LoganCoop/New-Paltz-Capstone-Project/calib_images/img1.jpg

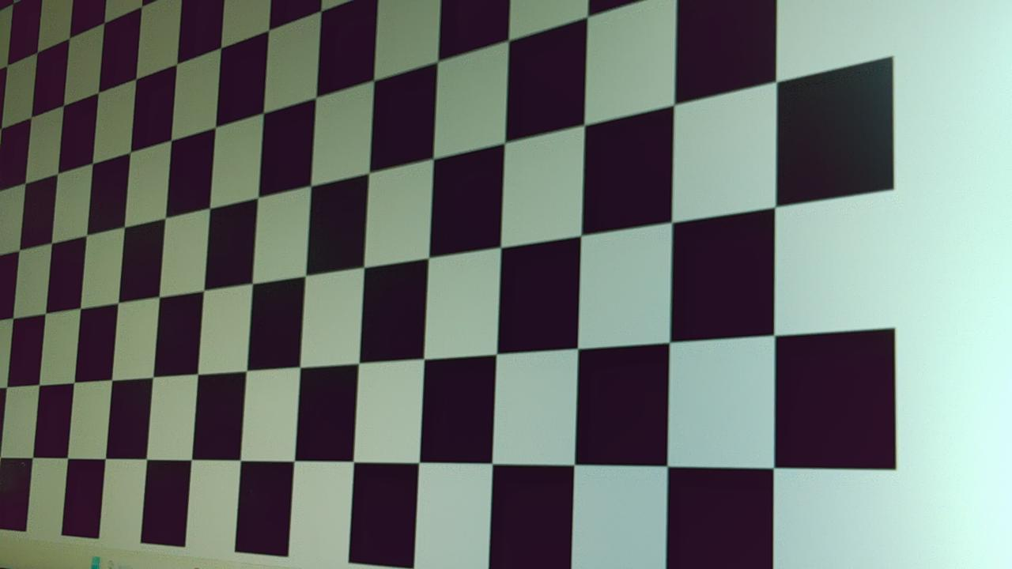
calib_images/img1.jpg
