LoganCoop/New-Paltz-Capstone-Project/calib_images/img01.jpg

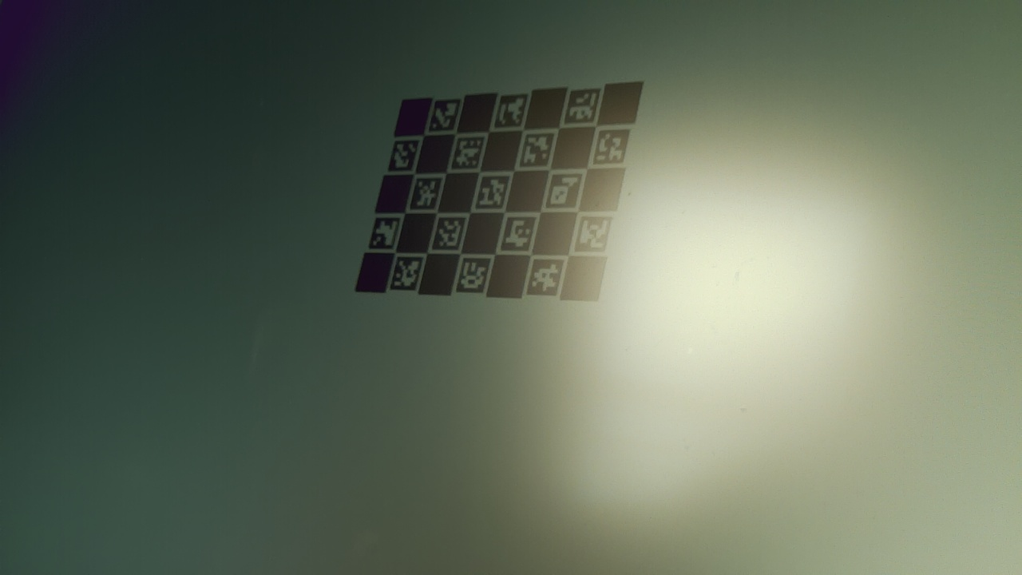
calib_images/img01.jpg
