LoganCoop/New-Paltz-Capstone-Project/calib_images/img2.jpg

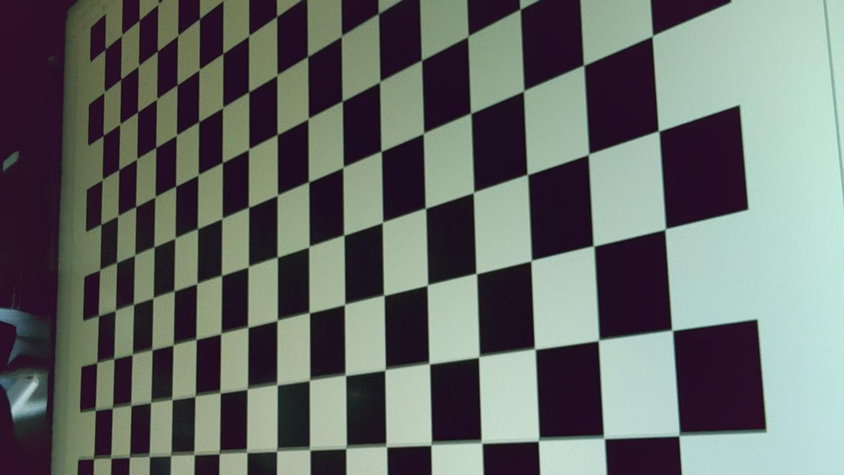
calib_images/img2.jpg
