LoganCoop/New-Paltz-Capstone-Project/calib_images/img03.jpg

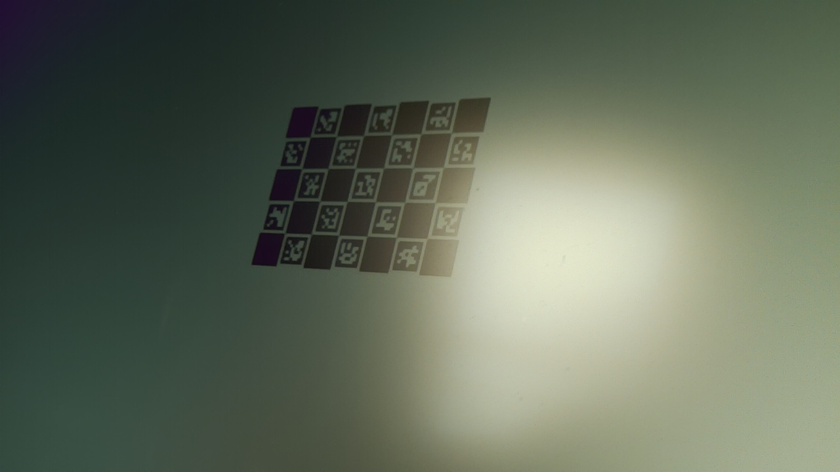
calib_images/img03.jpg
