LoganCoop/New-Paltz-Capstone-Project/calib_images/img3.jpg

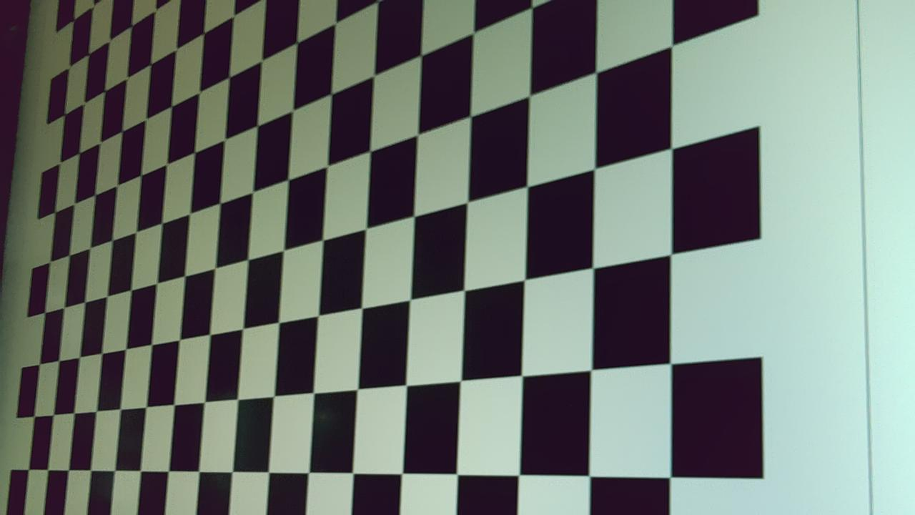
calib_images/img3.jpg
