LoganCoop/New-Paltz-Capstone-Project/calib_images/img4.jpg

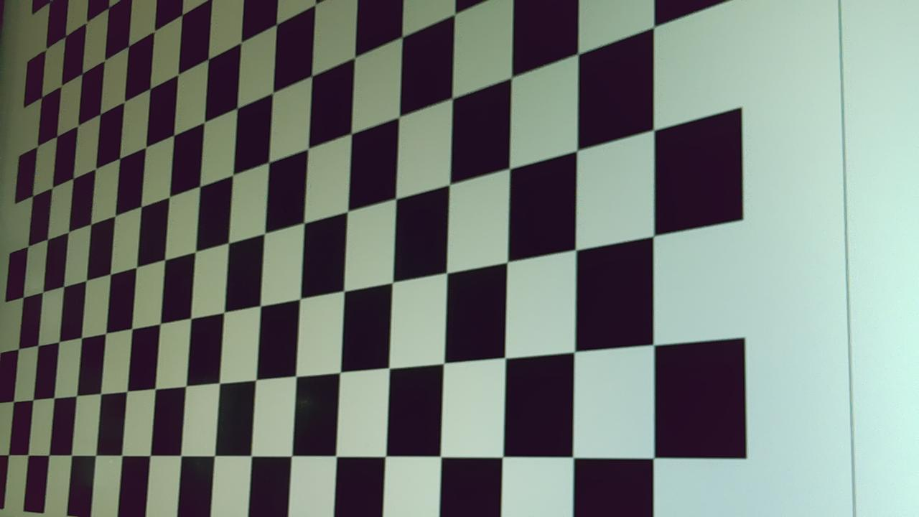
calib_images/img4.jpg
