LoganCoop/New-Paltz-Capstone-Project/calib_images/img5.jpg

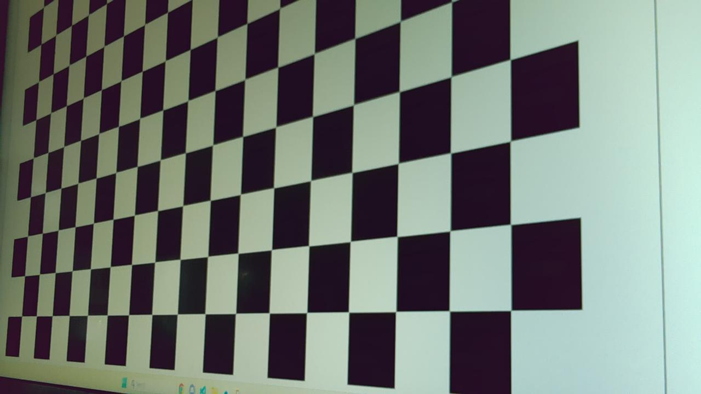
calib_images/img5.jpg
