LoganCoop/New-Paltz-Capstone-Project/calib_images/img05.jpg

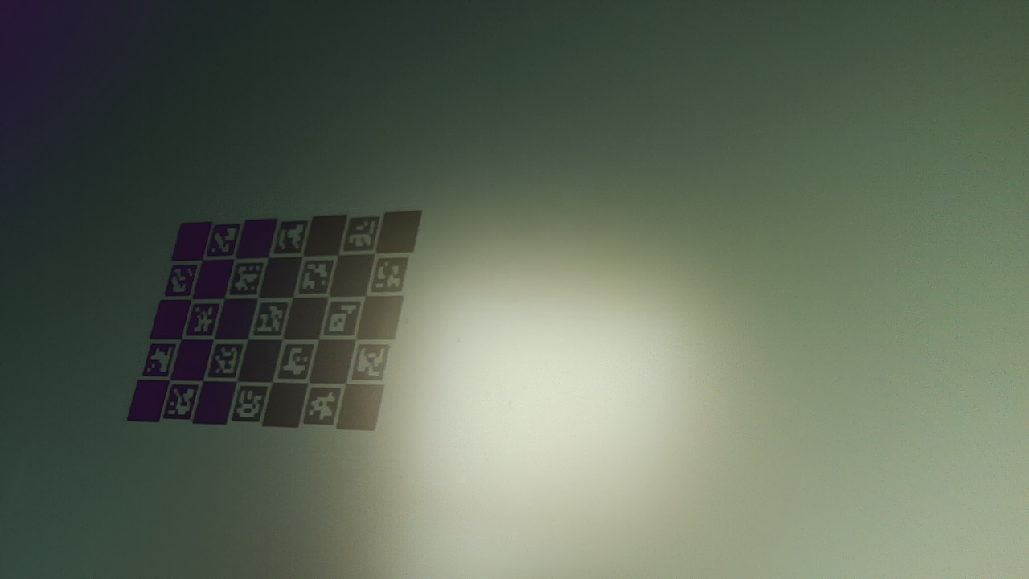
calib_images/img05.jpg
