LoganCoop/New-Paltz-Capstone-Project/calib_images/img06.jpg

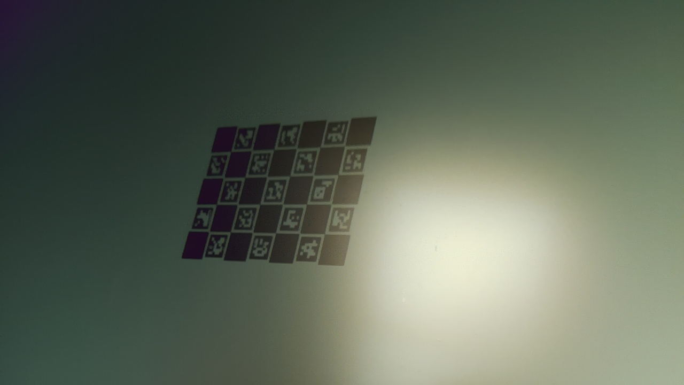
calib_images/img06.jpg
