LoganCoop/New-Paltz-Capstone-Project/calib_images/img6.jpg

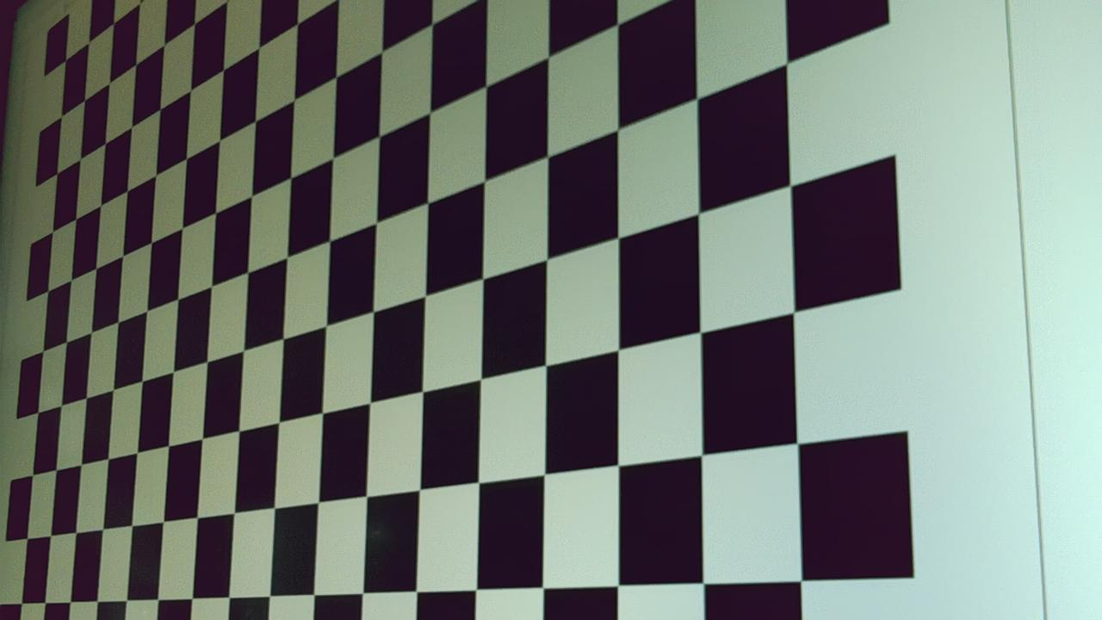
calib_images/img6.jpg
