LoganCoop/New-Paltz-Capstone-Project/calib_images/img07.jpg

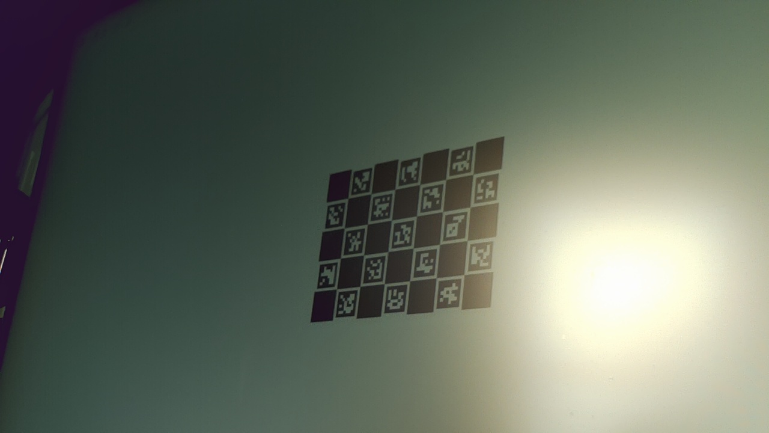
calib_images/img07.jpg
