LoganCoop/New-Paltz-Capstone-Project/calib_images/img7.jpg

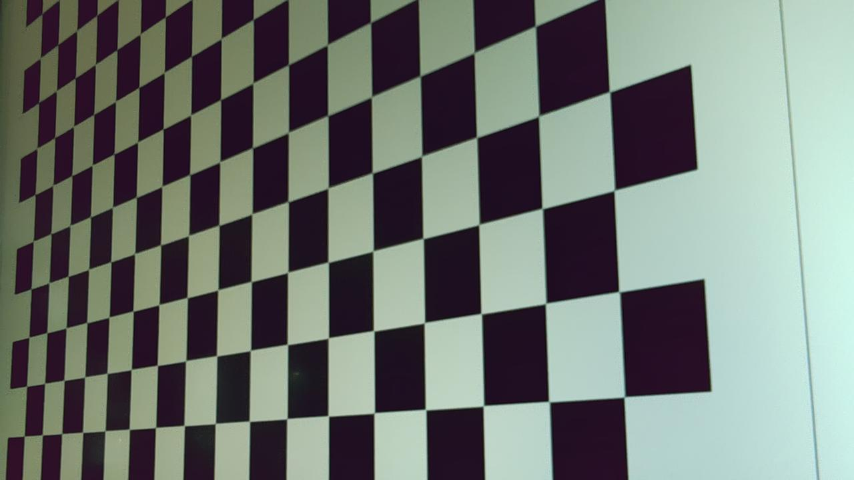
calib_images/img7.jpg
