LoganCoop/New-Paltz-Capstone-Project/calib_images/img8.jpg

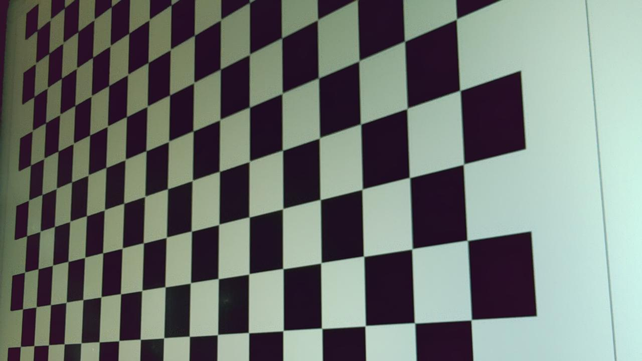
calib_images/img8.jpg
