LoganCoop/New-Paltz-Capstone-Project/calib_images/img08.jpg

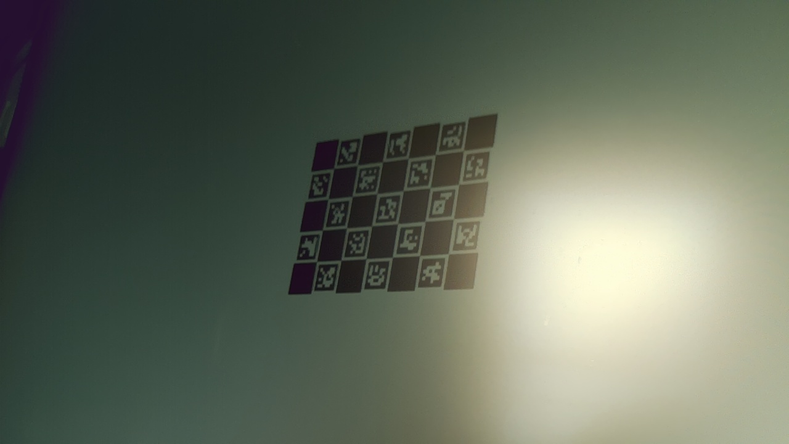
calib_images/img08.jpg
