LoganCoop/New-Paltz-Capstone-Project/calib_images/img9.jpg

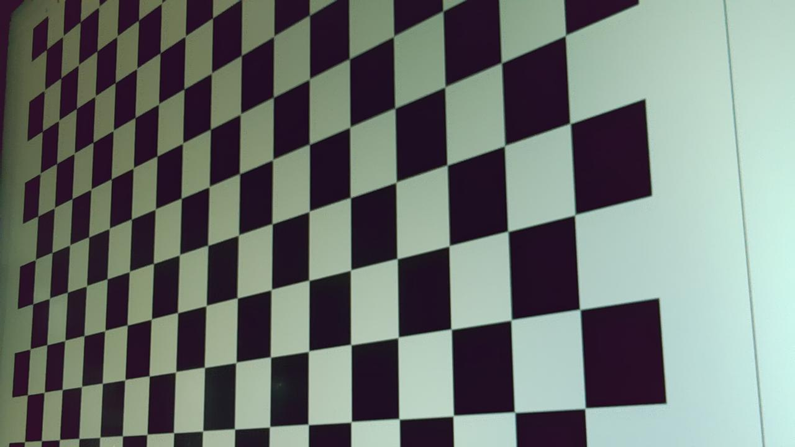
calib_images/img9.jpg
