LoganCoop/New-Paltz-Capstone-Project/calib_images/img09.jpg

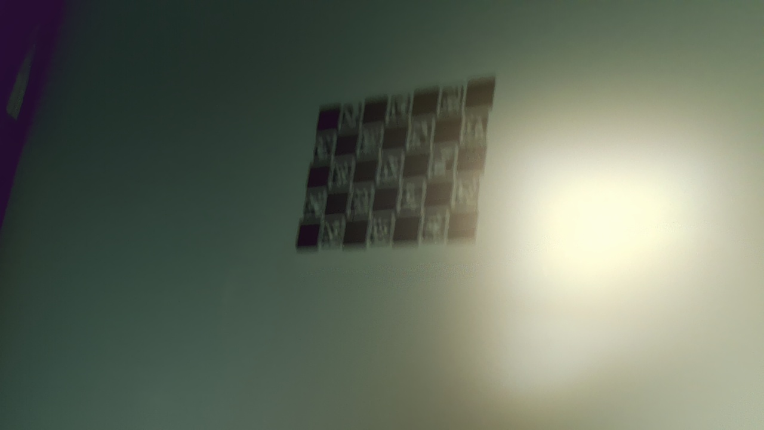
calib_images/img09.jpg
