LoganCoop/New-Paltz-Capstone-Project/calib_images/img10.jpg

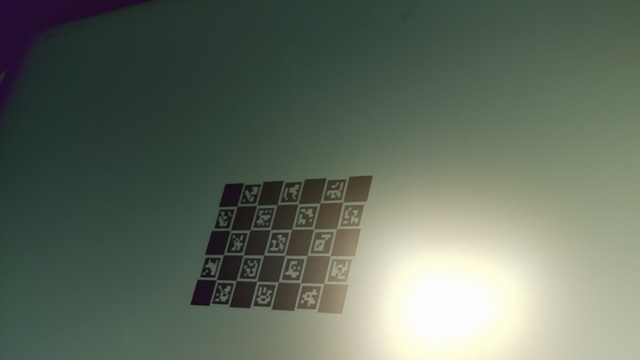
calib_images/img10.jpg
