LoganCoop/New-Paltz-Capstone-Project/calib_images/img11.jpg

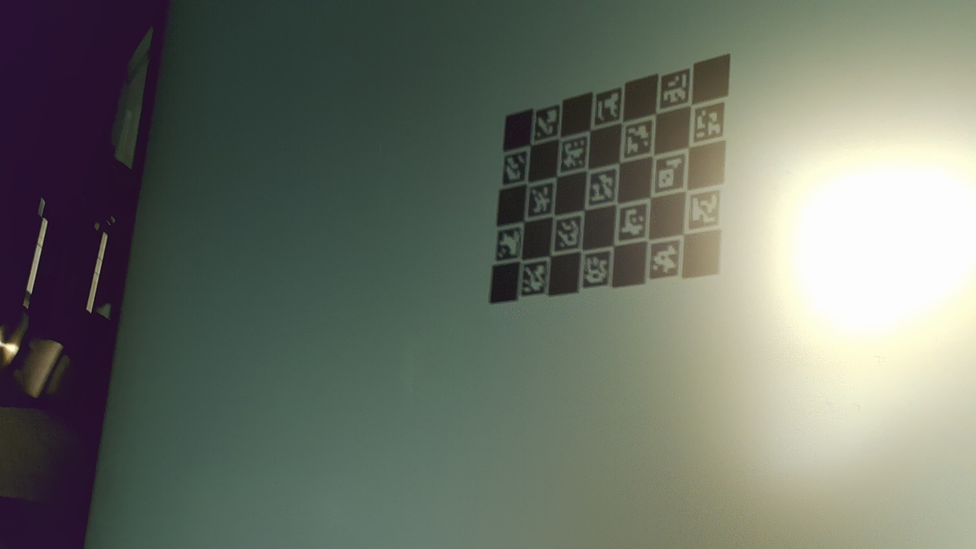
calib_images/img11.jpg
