LoganCoop/New-Paltz-Capstone-Project/calib_images/img12.jpg

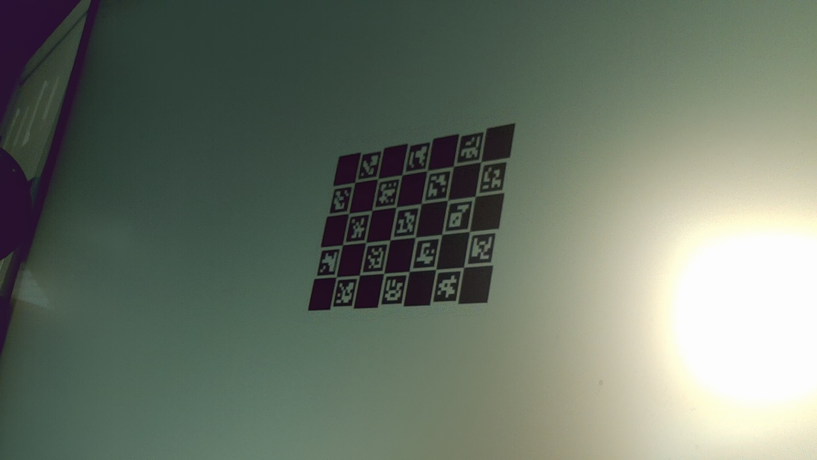
calib_images/img12.jpg
