LoganCoop/New-Paltz-Capstone-Project/calib_images/img14.jpg

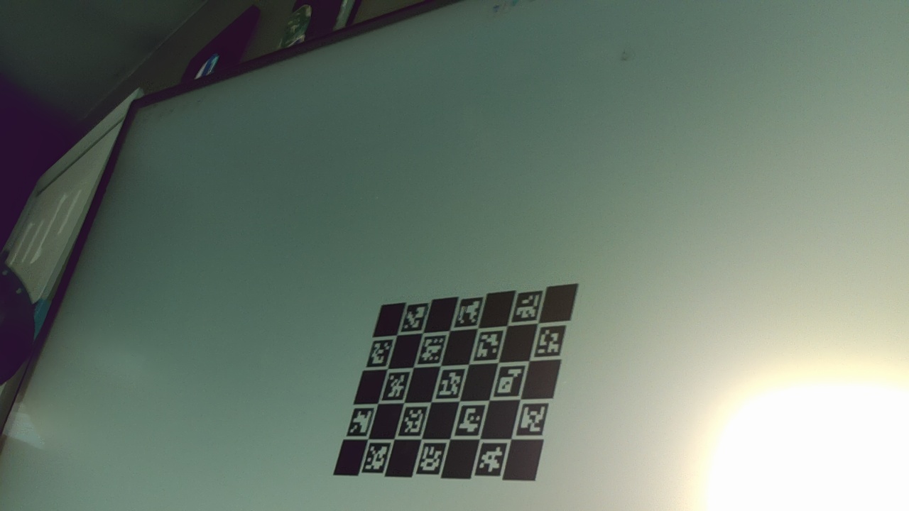
calib_images/img14.jpg
