LoganCoop/New-Paltz-Capstone-Project/calib_images/img15.jpg

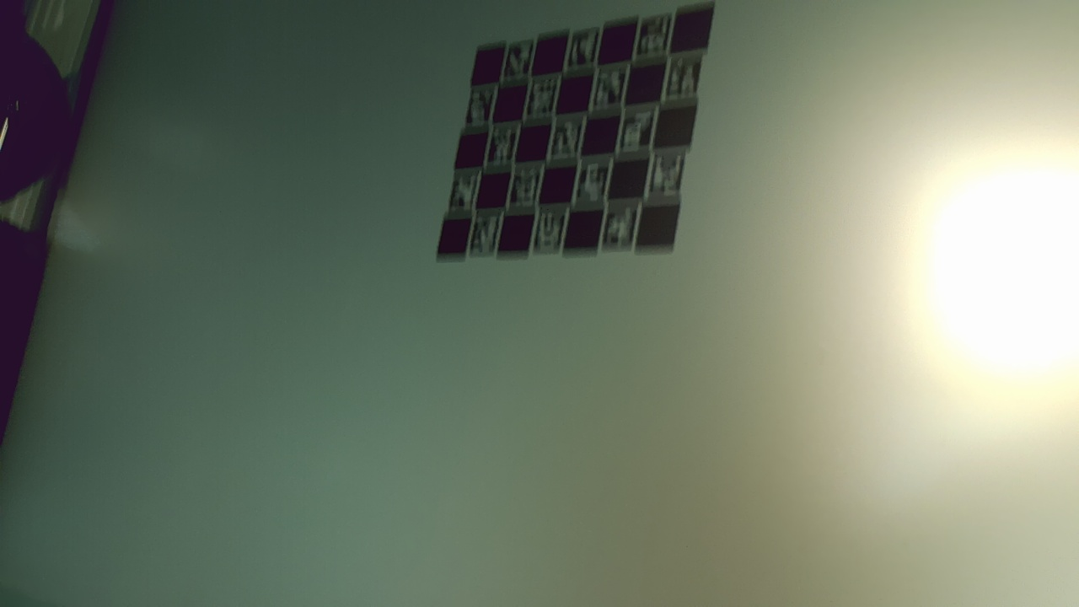
calib_images/img15.jpg
