LoganCoop/New-Paltz-Capstone-Project/calib_images/img100.jpg

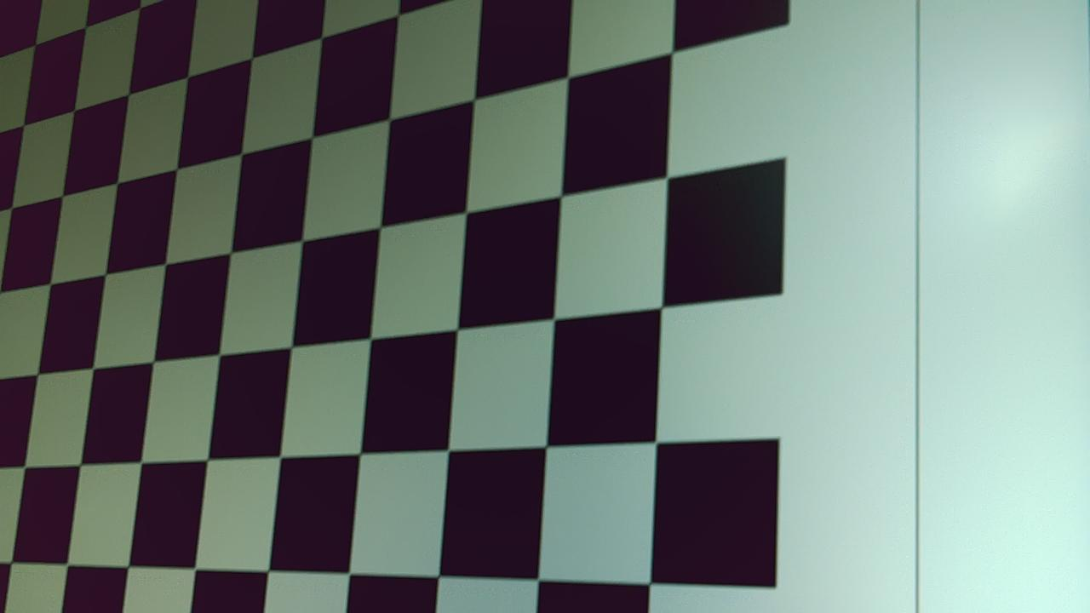
calib_images/img100.jpg
