LoganCoop/New-Paltz-Capstone-Project/calib_images/img101.jpg

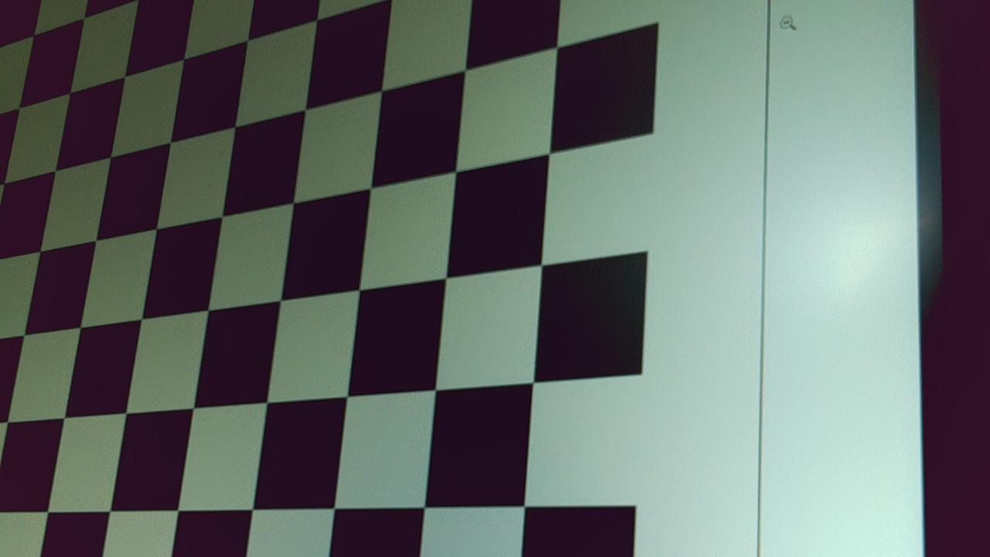
calib_images/img101.jpg
