LoganCoop/New-Paltz-Capstone-Project/calib_images/img102.jpg

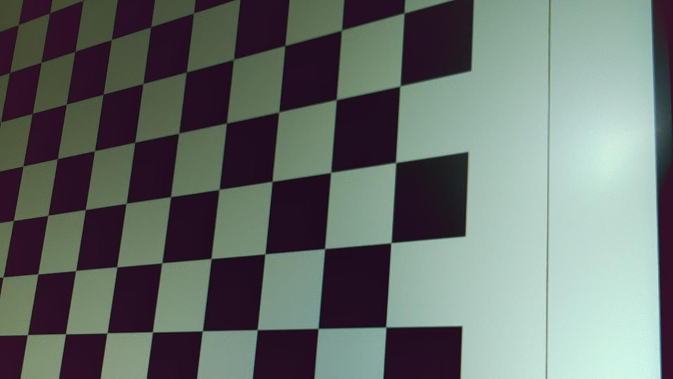
calib_images/img102.jpg
