LoganCoop/New-Paltz-Capstone-Project/calib_images/img103.jpg

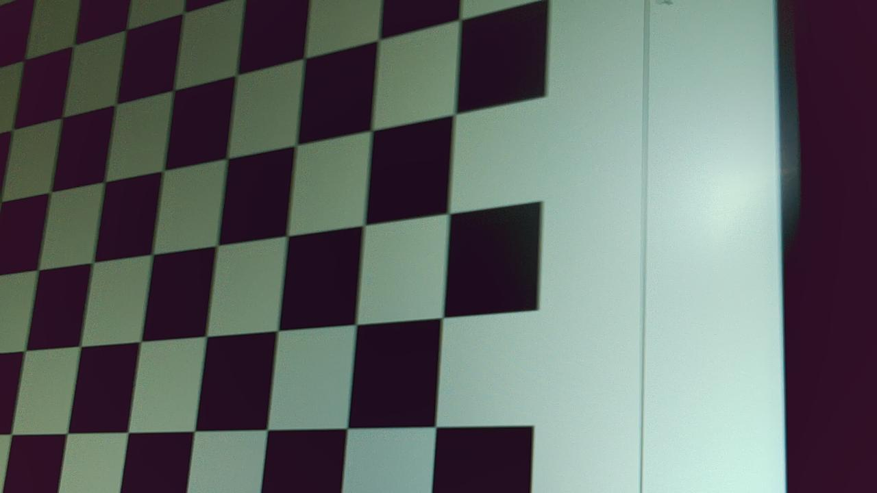
calib_images/img103.jpg
