LoganCoop/New-Paltz-Capstone-Project/calib_images/img104.jpg

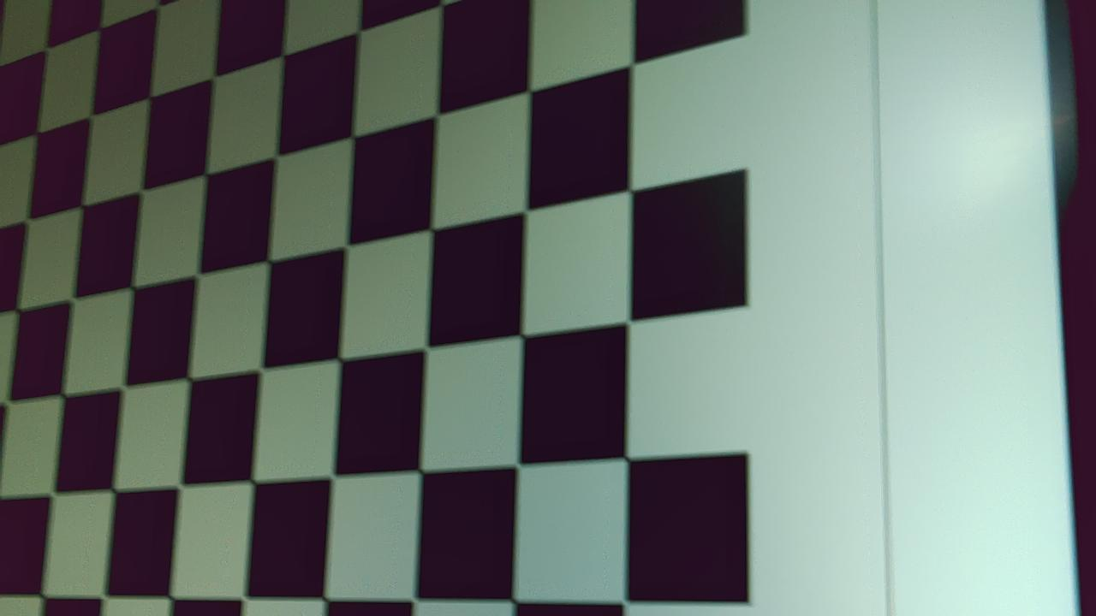
calib_images/img104.jpg
