LoganCoop/New-Paltz-Capstone-Project/presentation/Screenshot 2026-04-29 195957.png

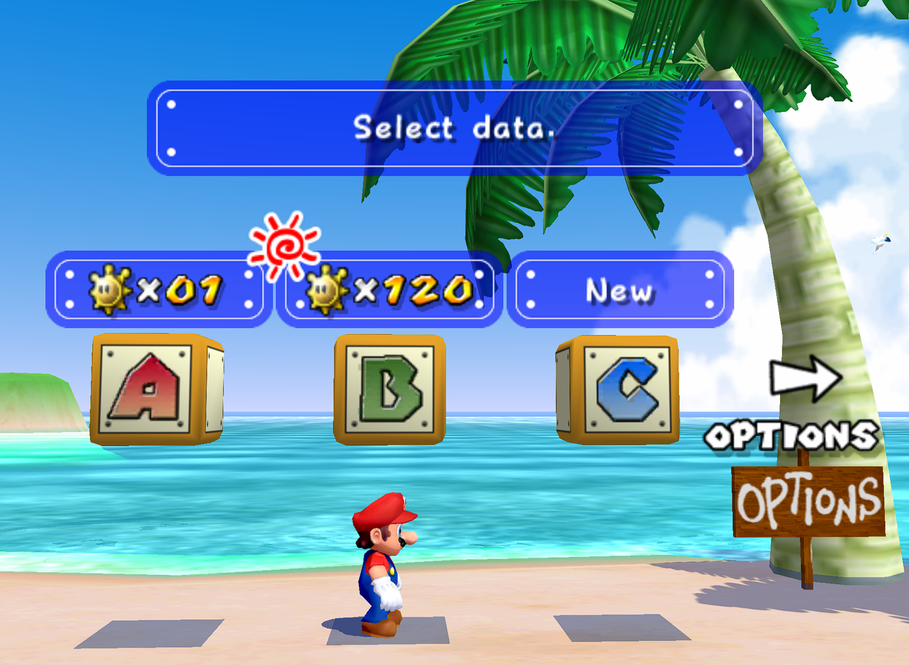
presentation/Screenshot 2026-04-29 195957.png
