LoganCoop/New-Paltz-Capstone-Project/tools/aruco_pose_demo.py

import argparse
import sys
import time

import numpy as np


def load_calibration(path):
    data = np.load(path)
    camera_matrix = data.get("camera_matrix")
    dist_coeffs = data.get("dist_coeffs")
    if camera_matrix is None or dist_coeffs is None:
        raise ValueError("Calibration file must contain camera_matrix and dist_coeffs.")
    return camera_matrix, dist_coeffs


def main():
    import socket
    import json

    # Build argument parser (include UDP options and camera options)
    parser = argparse.ArgumentParser(description="Detect ArUco markers with Pi Camera 3.")
    # UDP config for marker output (default to local aggregator)
    parser.add_argument("--udp-ip", default="127.0.0.1", help="Destination UDP IP for marker packets (default localhost)")
    parser.add_argument("--udp-port", type=int, default=6006, help="Destination UDP port for marker packets (default 6006)")
    sock = socket.socket(socket.AF_INET, socket.SOCK_DGRAM)
    parser.add_argument("--marker-length", type=float, default=0.05, help="Marker side length (meters)")
    parser.add_argument("--calib", default=None, help="Path to .npz with camera_matrix and dist_coeffs")
    parser.add_argument("--rate", type=float, default=10.0, help="Detection rate in Hz")
    parser.add_argument("--display", action="store_true", help="Show a live preview window")
    parser.add_argument("--width", type=int, default=1280, help="Camera capture width")
    parser.add_argument("--height", type=int, default=720, help="Camera capture height")
    parser.add_argument("--max-fps", type=float, default=30.0, help="Maximum camera FPS to request")
    parser.add_argument("--threaded", action="store_true", help="Use threaded capture to decouple capture and processing")
    parser.add_argument(
        "--backend",
        choices=["picamera2", "opencv", "rpicam"],
        default="opencv",
        help=(
            "Camera backend to use: 'picamera2', 'opencv' (VideoCapture),"
            " or 'rpicam' (VideoCapture pinned to a V4L2 device). Default: rpicam"
        ),
    )
    parser.add_argument(
        "--device",
        default="/dev/video0",
        help="Video device path or numeric index for OpenCV/rpicam backends (e.g. /dev/video0 or 0)",
    )
    args = parser.parse_args()

    use_picamera2 = args.backend == "picamera2"
    use_opencv = args.backend in ("opencv", "rpicam")

    if use_picamera2:
        try:
            from picamera2 import Picamera2
        except ImportError:
            print(
                "picamera2 is not installed. On Raspberry Pi OS, run: sudo apt install -y python3-picamera2",
                file=sys.stderr,
            )
            raise SystemExit(1)

    try:
        import cv2
    except ImportError:
        print(
            "OpenCV is not installed. On Raspberry Pi OS, run: sudo apt install -y python3-opencv",
            file=sys.stderr,
        )
        raise SystemExit(1)

    camera_matrix = None
    dist_coeffs = None
    if args.calib:
        camera_matrix, dist_coeffs = load_calibration(args.calib)

    # Initialize camera backend
    cap = None
    camera = None
    cap = None
    camera = None
    if use_picamera2:
        camera = Picamera2()
        config = camera.create_preview_configuration(main={"size": (args.width, args.height)})
        camera.configure(config)
        camera.start()
    elif use_opencv:
        # Use OpenCV VideoCapture for both 'opencv' and 'rpicam' backends.
        # Allow specifying device as '/dev/video0' or numeric index '0'.
        device = args.device
        try:
            dev_index = int(device)
        except Exception:
            dev_index = device

        api_preference = 0
        if hasattr(cv2, "CAP_V4L2"):
            api_preference = cv2.CAP_V4L2

        def try_open(dev):
            try:
                c = cv2.VideoCapture(dev, api_preference)
            except Exception:
                c = cv2.VideoCapture(dev)
            try:
                c.set(cv2.CAP_PROP_FRAME_WIDTH, args.width)
                c.set(cv2.CAP_PROP_FRAME_HEIGHT, args.height)
                # try to set fps
                try:
                    c.set(cv2.CAP_PROP_FPS, float(args.max_fps))
                except Exception:
                    pass
            except Exception:
                pass
            # test read
            ret, _ = c.read()
            if ret:
                return c
            try:
                c.release()
            except Exception:
                pass
            return None

        cap = try_open(dev_index)
        if cap is None:
            # probe /dev/video* list for a working device
            import glob

            candidates = sorted(glob.glob('/dev/video*'))
            for dev in candidates:
                if dev == str(dev_index):
                    continue
                cap = try_open(dev)
                if cap is not None:
                    print(f"Auto-selected video device: {dev}")
                    break
        if cap is None:
            # fallback to picamera2 if available
            try:
                from picamera2 import Picamera2  # type: ignore

                print("OpenCV VideoCapture failed; falling back to picamera2 backend")
                camera = Picamera2()
                config = camera.create_preview_configuration(main={"size": (args.width, args.height)})
                camera.configure(config)
                camera.start()
                use_picamera2 = True
            except Exception:
                raise SystemExit("No usable camera backend found (tried OpenCV and picamera2).")

    # Threaded capture helper (simple single-frame buffer)
    class FrameBuffer:
        def __init__(self):
            from threading import Lock

            self.lock = Lock()
            self.frame = None

        def put(self, f):
            with self.lock:
                self.frame = f

        def get(self):
            with self.lock:
                return self.frame

    fb = FrameBuffer()
    capture_thread = None
    if args.threaded:
        import threading

        def capture_loop():
            while True:
                try:
                    if use_picamera2 and camera is not None:
                        f = camera.capture_array()
                    elif cap is not None:
                        ret, f = cap.read()
                        if not ret:
                            f = None
                    else:
                        f = None
                    if f is not None and f.size != 0:
                        fb.put(f)
                except Exception:
                    pass

        capture_thread = threading.Thread(target=capture_loop, daemon=True)
        capture_thread.start()

    dictionary = cv2.aruco.getPredefinedDictionary(cv2.aruco.DICT_4X4_50)
    detector = cv2.aruco.ArucoDetector(dictionary)

    interval = 1.0 / max(args.rate, 0.1)
    try:
        while True:
            if use_picamera2:
                frame = camera.capture_array()
                if frame is None or frame.size == 0:
                    print("Warning: Empty frame captured from camera.", file=sys.stderr)
                    time.sleep(interval)
                    continue
            else:
                ret, frame = cap.read()
                if not ret or frame is None or frame.size == 0:
                    print("Warning: Empty frame captured from VideoCapture.", file=sys.stderr)
                    time.sleep(interval)
                    continue
            # Convert 4-channel (BGRA/RGBA) to 3-channel BGR if needed
            if len(frame.shape) == 3 and frame.shape[2] == 4:
                frame_bgr = cv2.cvtColor(frame, cv2.COLOR_BGRA2BGR)
            else:
                frame_bgr = frame
            gray = cv2.cvtColor(frame_bgr, cv2.COLOR_BGR2GRAY)
            corners, ids, _ = detector.detectMarkers(gray)

            marker_data = []
            if ids is not None and len(ids) > 0:
                ids_list = [int(x) for x in ids.flatten()]
                print(f"markers={ids_list}")

                if camera_matrix is not None and dist_coeffs is not None:
                    rvecs, tvecs, _ = cv2.aruco.estimatePoseSingleMarkers(
                        corners, args.marker_length, camera_matrix, dist_coeffs
                    )
                    for idx, marker_id in enumerate(ids_list):
                        tvec = tvecs[idx][0]
                        print(
                            f"id={marker_id} tvec_m=({tvec[0]:.3f}, {tvec[1]:.3f}, {tvec[2]:.3f})"
                        )
                        marker_data.append({
                            "id": marker_id,
                            "tvec": [float(tvec[0]), float(tvec[1]), float(tvec[2])]
                        })

            # Send marker data over UDP if any markers detected
            if marker_data:
                packet = {"timestamp": time.time(), "markers": marker_data}
                try:
                    msg = json.dumps(packet).encode('utf-8')
                    print("UDP packet:", msg)
                    sock.sendto(msg, (args.udp_ip, args.udp_port))
                    print(f"Sent UDP packet to {args.udp_ip}:{args.udp_port}")
                except Exception as e:
                    print(f"Warning: Failed to send UDP packet: {e}", file=sys.stderr)

            if args.display and frame is not None and frame.size != 0:
                # Use frame_bgr for display (guaranteed 3-channel BGR)
                frame_disp = frame_bgr
                try:
                    cv2.aruco.drawDetectedMarkers(frame_disp, corners, ids)
                except Exception as e:
                    print(f"Warning: drawDetectedMarkers failed: {e}", file=sys.stderr)
                cv2.imshow("Aruco", frame_disp)
                if cv2.waitKey(1) & 0xFF == ord("q"):
                    break

            time.sleep(interval)
    finally:
        if camera is not None:
            try:
                camera.stop()
            except Exception:
                pass
        if cap is not None:
            try:
                cap.release()
            except Exception:
                pass
        if args.display:
            cv2.destroyAllWindows()


if __name__ == "__main__":
    main()
